gerdb/go-kart-control/java/src/com/rapplogic/xbee/api/XBee.java

/**
 * Copyright (c) 2008 Andrew Rapp. All rights reserved.
 *  
 * This file is part of XBee-API.
 *  
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
 * You should have received a copy of the GNU General Public License
 * along with XBee-API.  If not, see <http://www.gnu.org/licenses/>.
 */

package com.rapplogic.xbee.api;

import java.io.IOException;
import java.util.LinkedList;
import java.util.List;
import java.util.concurrent.TimeUnit;

import com.rapplogic.xbee.RxTxSerialComm;
import com.rapplogic.xbee.XBeeConnection;
import com.rapplogic.xbee.util.ByteUtils;
import com.sebulli.gokart.Logger;

import static com.sebulli.gokart.Translate._;
/**
 * This is an API for communicating with Digi XBee 802.15.4 and ZigBee radios
 * via the serial port
 * <p/>
 * @author Andrew Rapp <andrew.rapp at gmail>
 * 
 */
public class XBee implements IXBee {

	private final static Logger log = Logger.getLogger(XBee.class);
	
	// object to synchronize on to protect access to sendPacket
	private Object sendPacketBlock = new Object();
	private XBeeConnection xbeeConnection;
	private InputStreamThread parser;	
	private XBeeConfiguration conf;
	private RxTxSerialComm serial = null;
	
	public XBee() {
		this.conf = new XBeeConfiguration().withMaxQueueSize(100).withStartupChecks(true);
		
		Runtime.getRuntime().addShutdownHook(new Thread() {
		    public void run() { 
		    	if (isConnected()) {
		    		log.info("ShutdownHook is closing connection");
		    		close();
		    	}
		    }
		});
	}

	public XBee(XBeeConfiguration conf) {
		this.conf = conf;
	}
	
	/**
	 * Generate a reset on DTR line
	 */
	public void reset() throws XBeeException {
		
		try {
			if (serial != null) {
				serial.serialPort.setDTR(true);
				Thread.sleep(1000);
				serial.serialPort.setDTR(false);
				Thread.sleep(500);
			}
		} catch (InterruptedException e) {
		}
	}
	
	/**
	 * Set the XBee module into AP2 Mode
	 */
	public void setAP2Mode() throws XBeeException {
		// Set AP2 mode
		try {
			Thread.sleep(1100);
			parser.setIgnoreRX(true);
			this.sendPacket("+++");
			Thread.sleep(1100);
			this.sendPacket("ATAP 2\r");
			Thread.sleep(200);
			this.sendPacket("ATCN\r");
			Thread.sleep(200);
			parser.setIgnoreRX(false);
		} catch (InterruptedException e) {
		} catch (IOException e2) {
			e2.printStackTrace();
			throw new XBeeException(_("IO Exception during initializing the XBee module"));
		}	
	}
	
	private void doStartupChecks() throws XBeeException {
		// Perform startup checks
		try {				
			
			AtCommandResponse ap = this.sendAtCommand(new AtCommand("AP"));
			
			if (!ap.isOk()) {
				throw new XBeeException("Attempt to query AP parameter failed");
			}
			
			log.log("Connected to XBee module");
			
			if (ap.getValue()[0] != 2) {
				log.warn("XBee radio is in API mode without escape characters (AP=1).  The radio must be configured in API mode with escape bytes (AP=2) for use with this library.");
				
				log.log("Attempting to set AP to 2");
				ap = this.sendAtCommand(new AtCommand("AP", 2));
				
				if (ap.isOk()) {
					log.log("Successfully set AP mode to 2.  This setting will not persist a power cycle without the WR (write) command");	
				} else {
					throw new XBeeException("Attempt to set AP=2 failed");
				}
			} else {
				log.log("Radio is in correct AP mode (AP=2)");
			}

			ap = this.sendAtCommand(new AtCommand("HV"));
			
			if (!ap.isOk()) {
				throw new XBeeException("Attempt to query HV parameter failed");
			}
			
			if (ap.isOk()) {
				switch (ap.getValue()[0]) {
				case 0x17:
					log.log("XBee radio is Series 1");
					break;
				case 0x18:
					log.log("XBee radio is Series 1 Pro");
					break;
				case 0x19:
					log.log("XBee radio is Series 2");
					break;
				case 0x1a:
					log.log("XBee radio is Series 2 Pro");
					break;
				case 0x1d:
					log.log("XBee radio is Series Pro 868");
					break;
				default:
					log.warn("Unknown radio type (HV): " + ap.getValue()[0]);
				}
			}	
			
			AtCommandResponse vr = this.sendAtCommand(new AtCommand("VR"));
			
			if (vr.isOk()) {
				log.log("Firmware version is " + ByteUtils.toBase16(vr.getValue()));
			}
			
			AtCommandResponse sh = this.sendAtCommand(new AtCommand("SH"));
			
			String ah="", al="";
			if (sh.isOk()) {
				ah = ByteUtils.toBase16(sh.getValue());
				ah = ah.replace("0x", "");
				ah = ah.replace(",", "");
				ah = ah.toUpperCase();
			}
			
			AtCommandResponse sl = this.sendAtCommand(new AtCommand("SL"));
			
			if (sl.isOk()) {
				al = ByteUtils.toBase16(sl.getValue());
				al = al.replace("0x", "");
				al = al.replace(",", "");
				al = al.toUpperCase();
			}
			log.log("Serial address: " + ah + " " +al);
			
			this.clearResponseQueue();
			
		} catch (XBeeTimeoutException ex) {
			throw new XBeeException(_("No connection to XBee module. Is it in API mode (AP=2)?"));
		}	
	}
	
	/**
	 * If XBeeConnection.startUpChecks is set to true (default), this method will check if the AP parameter
	 * is set correctly and attempt to update if AP=1.  If AP=0 (Transparent mode), an
	 * exception will be thrown.
	 */
	public void open(String port, int baudRate) throws XBeeException {
		try {
			if (this.isConnected()) {
				throw new IllegalStateException("Cannot open new connection -- existing connection is still open.  Please close first");
			}
			
			serial = new RxTxSerialComm();
			serial.openSerialPort(port, baudRate);
			serial.serialPort.setDTR(false);
			log.log("Serial port opened:" + " " + port);
			
			this.initConnection(serial);
		} catch (XBeeException e) {
			throw e;
		} catch (Exception e) {		
			throw new XBeeException(e);
		}
	}
	
	/**
	 * Allows a protocol specific implementation of XBeeConnection to be used instead of the default RXTX connection.
	 * The connection must already be established as the interface has no means to do so.
	 */
	public void initProviderConnection(XBeeConnection connection) throws XBeeException {
		if (this.isConnected()) {
			throw new IllegalStateException("Cannot open new connection -- existing connection is still open.  Please close first");
		}
		
		initConnection(connection);
	}
	
	private void initConnection(XBeeConnection conn) throws XBeeException {
		try {			
			this.xbeeConnection = conn;
			
			parser = new InputStreamThread(this.xbeeConnection, conf);
			
			// Set the module into AP2 mode
			setAP2Mode();
			
			// startup heuristics
			if (conf.isStartupChecks()) {
				this.doStartupChecks();
			}
		} catch (XBeeException e) {
			throw e;
		} catch (Exception e) {		
			throw new XBeeException(e);
		}
	}

	public void addPacketListener(PacketListener packetListener) { 
		if (parser == null) {
			throw new IllegalStateException("No connection");
		}
		
		synchronized (parser.getPacketListenerList()) {
			this.parser.getPacketListenerList().add(packetListener);	
		}
	}

	public void removePacketListener(PacketListener packetListener) {
		if (parser == null) {
			throw new IllegalStateException("No connection");
		}
		
		synchronized (parser.getPacketListenerList()) {
			this.parser.getPacketListenerList().remove(packetListener);
		}
	}
	
	public void removeAllPacketListener() {
		if (parser == null) {
			throw new IllegalStateException("No connection");
		}
		
		synchronized (parser.getPacketListenerList()) {
			this.parser.getPacketListenerList().clear();
		}
	}
	
	public void sendRequest(XBeeRequest request) throws IOException {
		log.info("Sending request to XBee: " + request);
		this.sendPacket(request.getXBeePacket());
	}
	
	/** 
	 * It's possible for packets to get interspersed if multiple threads send simultaneously.  
	 * This method is not thread-safe because doing so would introduce a synchronized performance penalty 
	 * for the vast majority of users that will not never need thread safety.
	 * That said, it is responsibility of the user to provide synchronization if multiple threads are sending.
	 * 
	 * Not thread safe.
	 *  
	 * @param packet
	 * @throws IOException
	 */
	public void sendPacket(XBeePacket packet) throws IOException {	
		this.sendPacket(packet.getByteArray());
	}
	
	/** 
	 * send a packet as string
	 * Not thread safe.
	 *  
	 * @param packet
	 * @throws IOException
	 */
	public void sendPacket(String packet) throws IOException {
		int[] ints = new int[packet.getBytes().length];
		int i=0;
		for (byte  b : packet.getBytes()) {
			ints[i] = b;
			i++;
		}
		this.sendPacket(ints);
	}
	
	/**
	 * This exists solely for the XMPP project.  Use sendRequest instead
	 * 
	 * Not Thread Safe
	 * 
	 * @param packet
	 * @throws RuntimeException when serial device is disconnected
	 */
	public void sendPacket(int[] packet)  throws IOException {
		// TODO should we synchronize on read lock so we are sending/recv. simultaneously?
		// TODO call request listener with byte array
		
		if (!this.isConnected()) {
			throw new RuntimeException("XBee is not connected");
		}
		
		log.info("sending packet to XBee " + ByteUtils.toBase16(packet));	

        for (int aPacket : packet) {
        	xbeeConnection.getOutputStream().write(aPacket);
        }

        xbeeConnection.getOutputStream().flush();
	}

	/**
	 * Sends an XBeeRequest though the XBee interface in an asynchronous manner, such that
	 * it will return immediately, without waiting for a response.
	 * Refer to the getResponse method for obtaining a response
	 * 
	 * Not thread safe
	 * 
	 * @param request
	 * @throws XBeeException
	 */
	public void sendAsynchronous(XBeeRequest request) throws XBeeException {

		try {
			this.sendRequest(request);			
		} catch (Exception e) {
			throw new XBeeException(e);
		}
	}

	/**
	 * Uses sendSynchronous to send an AtCommand and collect the response
	 * <p/>
	 * Timeout value is fixed at 5 seconds
	 * 
	 * @deprecated Use this.sendSynchronous(command, timeout);
	 * @param command
	 * @return
	 * @throws XBeeException
	 */
	public AtCommandResponse sendAtCommand(AtCommand command) throws XBeeException {
		return (AtCommandResponse) this.sendSynchronous(command, 5000);
	}
	
	/**
	 * Synchronous method for sending an XBeeRequest and obtaining the 
	 * corresponding response (response that has same frame id).
	 * <p/>
	 * This method returns the first response object with a matching frame id, within the timeout
	 * period, so it is important to use a unique frame id (relative to previous subsequent requests).
	 * <p/>
	 * This method must only be called with requests that receive a response of
	 * type XBeeFrameIdResponse.  All other request types will timeout.
	 * <p/>
	 * Keep in mind responses received here will also be available through the getResponse method
	 * and the packet listener.  If you would prefer to not have these responses added to the response queue,
	 * you can add a ResponseQueueFilter via XBeeConfiguration to ignore packets that are sent in response to
	 * a request.  Another alternative is to call clearResponseQueue prior to calling this method.
	 * <p/>
	 * It is recommended to use a timeout of at least 5 seconds, since some responses can take a few seconds or more
	 * (e.g. if remote radio is not powered on).
	 * <p/>
	 * This method is thread-safe 
	 * 
	 * @param xbeeRequest
	 * 
	 * @return
	 * @throws XBeeException 
	 * @throws XBeeTimeoutException thrown if no matching response is identified
	 */
	public XBeeResponse sendSynchronous(final XBeeRequest xbeeRequest, int timeout) throws XBeeTimeoutException, XBeeException {		
		if (xbeeRequest.getFrameId() == XBeeRequest.NO_RESPONSE_FRAME_ID) {
			throw new XBeeException("Frame Id cannot be 0 for a synchronous call -- it will always timeout as there is no response!");
		}		

		PacketListener pl = null;
		
		try {
			final List<XBeeResponse> container = new LinkedList<XBeeResponse>();

			// this makes it thread safe -- prevents multiple threads from writing to output stream simultaneously
			synchronized (sendPacketBlock) {
				this.sendRequest(xbeeRequest);	
			}
			
			pl = new PacketListener() {
				// TODO handle error response as well
				public void processResponse(XBeeResponse response) {
					if (response instanceof XBeeFrameIdResponse && ((XBeeFrameIdResponse)response).getFrameId() == xbeeRequest.getFrameId()) {
					
						// frame id matches -- yay we found it
						container.add(response);
						synchronized(container) {
							container.notify();	
						}
						
					}
				}
			};
			
			this.addPacketListener(pl);
			
			synchronized (container) {
				if (container.size() == 0) {
					try {
						container.wait(timeout);
					} catch (InterruptedException e) { }
				}
			}
			if (container.size() == 0) {
				// we didn't find a matching packet
				throw new XBeeTimeoutException();
			}
			
			return (XBeeResponse) container.get(0);
		} catch (IOException io) {
			throw new XBeeException(io);
		} finally {
			if (pl != null) {
				this.removePacketListener(pl);
			}
		}
	}
	
	/**
	 * Uses sendSynchronous timeout defined in XBeeConfiguration (default is 5000ms)
	 */
	public XBeeResponse sendSynchronous(final XBeeRequest request) throws XBeeTimeoutException, XBeeException {		
		return this.sendSynchronous(request, conf.getSendSynchronousTimeout());
	}
	
		
	/**
	 * Same as getResponse(int) but does not timeout.
	 * It's highly recommend that you always use a timeout because
	 * if the serial connection dies under certain conditions, you will end up waiting forever!
	 * <p/>
	 * Consider using the PacketListener for asynchronous (non-blocking) behavior
	 * 
	 * @return
	 * @throws XBeeException 
	 */
	public XBeeResponse getResponse() throws XBeeException {
		return getResponseTimeout(null);
	}
	
	/**
	 * This method returns an XBeeResponse from the queue, if available, or
	 * waits up to "timeout" milliseconds for a response.
	 * <p/>
	 * There are three possible outcomes:
	 * <p/>
	 * 1.  A packet is returned within "timeout" milliseconds <br/>
	 * 2.  An XBeeTimeoutException is thrown (i.e. queue was empty for duration of timeout) <br/>
	 * 3.  Null is returned if timeout is 0 and queue is empty. <br/>
	 * <p/>
	 * @param timeout milliseconds to wait for a response.  A value of zero disables the timeout
	 * @return
	 * @throws XBeeException
	 * @throws XBeeTimeoutException if timeout occurs before a response is received
	 */
	public XBeeResponse getResponse(int timeout) throws XBeeException, XBeeTimeoutException {
		return this.getResponseTimeout(timeout);
	}
	
	private XBeeResponse getResponseTimeout(Integer timeout) throws XBeeException, XBeeTimeoutException {
		XBeeResponse response;
		try {
			if (timeout != null) {
				response = parser.getResponseQueue().poll(timeout, TimeUnit.MILLISECONDS);	
			} else {
				response = parser.getResponseQueue().take();
			}
		} catch (InterruptedException e) {
			throw new XBeeException("Error while attempting to remove packet from queue", e);
		}
		
		if (response == null && timeout > 0) {
			throw new XBeeTimeoutException();
		}
		
		return response;
	}
	
	
	/**
	 * Shuts down RXTX and packet parser thread
	 */
	public void close() {		

		if (!this.isConnected()) {
			throw new IllegalStateException("XBee is not connected");
		}
		
		// shutdown parser thread
		if (parser != null) {
			parser.setDone(true);
			// interrupts thread, if waiting.  does not interrupt thread if blocking on read
			// serial port close will be closed prior to thread exit
			parser.interrupt();
		}
		
		try {
			this.xbeeConnection.getOutputStream().close();
		} catch (IOException e) {
			log.warn("Failed to close output stream", e);
			throw new IllegalStateException("Failed to close output stream");
		}
		
		parser = null;
		xbeeConnection = null;
	}

	/**
	 * Indicates if serial port connection has been established.
	 * The open method may be called if true it returned
	 * 
	 * @return
	 */
	public boolean isConnected() {
		try {
			if (parser.getXBeeConnection().getInputStream() != null && parser.getXBeeConnection().getOutputStream() != null) {
				return true;
			}
			
			return false;
		} catch (Exception e) {
			return false;
		}
	}
	
	// TODO move to its own class
	private int sequentialFrameId = 0xff;
	
	public int getCurrentFrameId() {
		// TODO move to separate class (e.g. FrameIdCounter)
		return sequentialFrameId;
	}
	
	/**
	 * This is useful for obtaining a frame id when composing your XBeeRequest.
	 * It will return frame ids in a sequential manner until the maximum is reached (0xff)
	 * and it flips to 1 and starts over.
	 * 
	 * Not Thread-safe
	 * 
	 * @return
	 */
	public int getNextFrameId() {
		if (sequentialFrameId == 0xff) {
			// flip
			sequentialFrameId = 1;
		} else {
			sequentialFrameId++;
		}
		
		return sequentialFrameId;
	}
	
	/**
	 * Updates the frame id.  Any value between 1 and ff is valid
	 * 
	 * @param val
	 * Jan 24, 2009
	 */
	public void updateFrameId(int val) {
		if (val <=0 || val > 0xff) {
			throw new IllegalArgumentException("invalid frame id");
		}
		
		this.sequentialFrameId = val;
	}		
	
	/**
	 * Removes all packets off of the response queue
	 */
	public void clearResponseQueue() {
		parser.getResponseQueue().clear();
	}
}
